kirillstp/ffone/drawings/front assembly/front bracket.stl

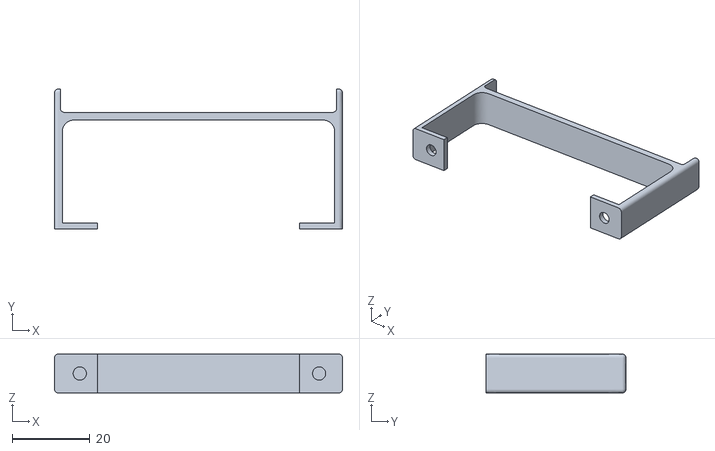
[picture p18: CAD file, 2019-01-05]
drawings/front assembly/front bracket.stl
74.0 x 36.0 x 10.0
